BusKill/usb-a-magnetic-breakaway/Goldfishlaser Version/CAD Files/usbamagb_v03.1b.png

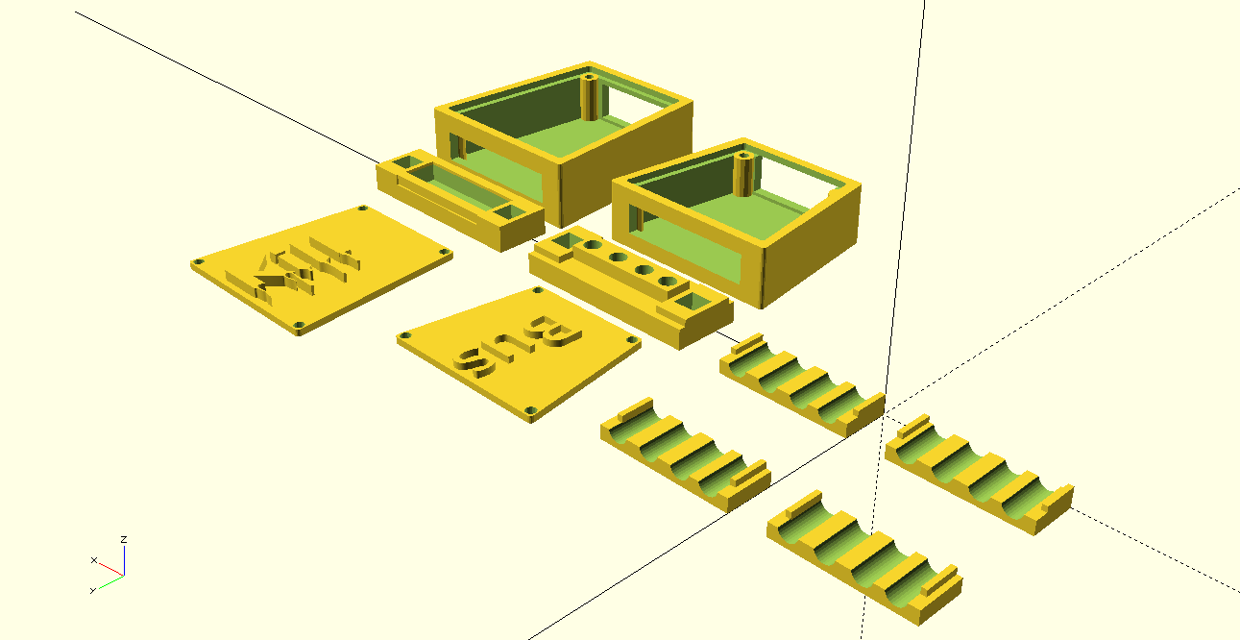
Goldfishlaser Version/CAD Files/usbamagb_v03.1b.png
