BusKill/usb-a-magnetic-breakaway/supplier/shenzen_qh_industrial_co/2021-05-24/una2.png

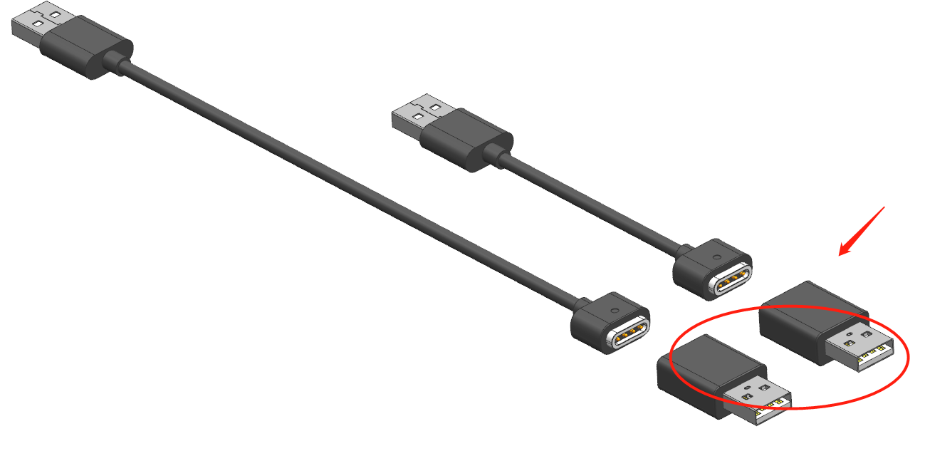
supplier/shenzen_qh_industrial_co/2021-05-24/una2.png
