BusKill/usb-a-magnetic-breakaway/supplier/shenzen_qh_industrial_co/2021-06-10/buskill_custom_female_3d_screenshot.jpg

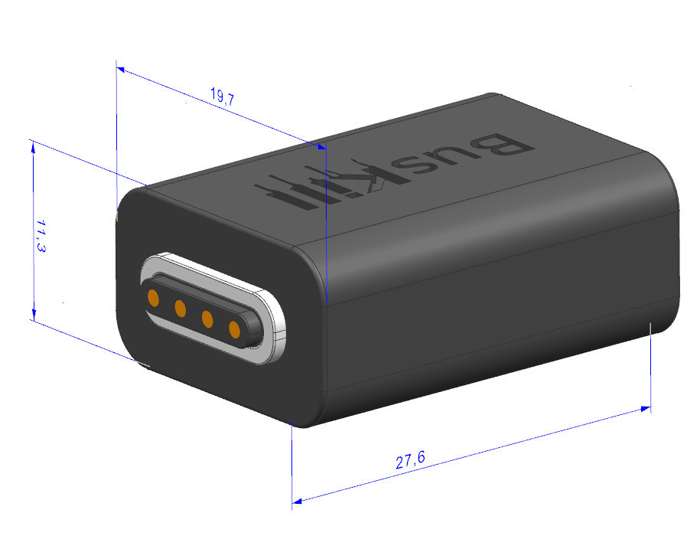
supplier/shenzen_qh_industrial_co/2021-06-10/buskill_custom_female_3d_screenshot.jpg
