BusKill/usb-a-magnetic-breakaway/supplier/shenzen_qh_industrial_co/2021-10-06/20211006_buskill_mold.jpg

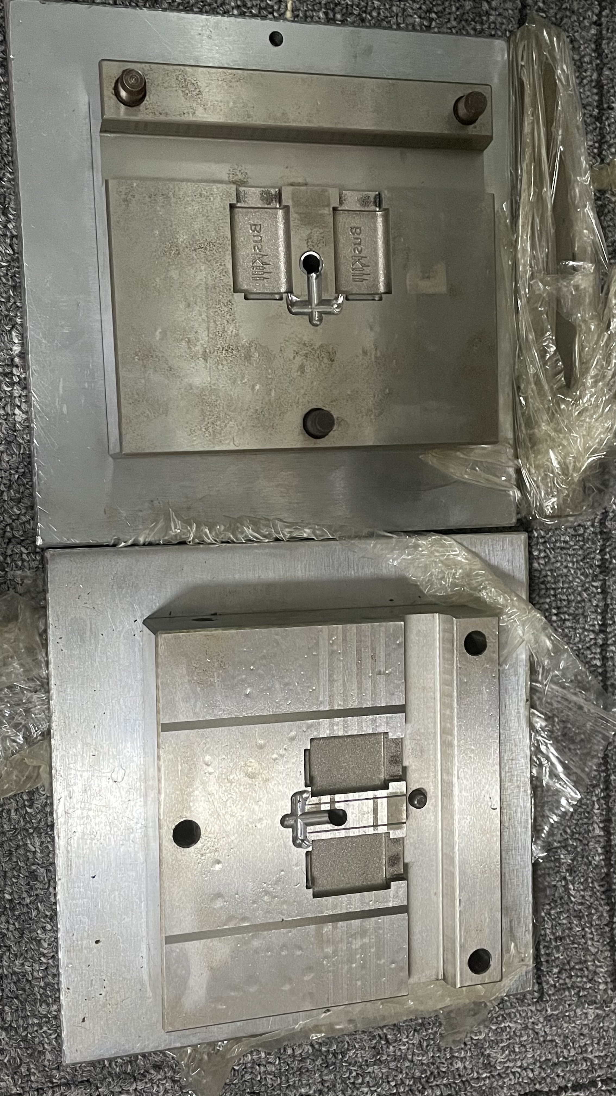
supplier/shenzen_qh_industrial_co/2021-10-06/20211006_buskill_mold.jpg
