BusKill/usb-a-magnetic-breakaway/supplier/shenzen_qh_industrial_co/2021-12-04/202112_buskill_sample1b.jpg

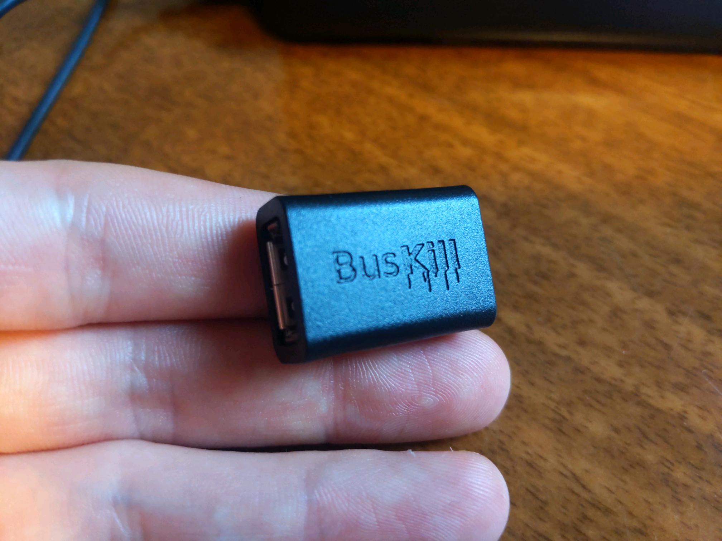
supplier/shenzen_qh_industrial_co/2021-12-04/202112_buskill_sample1b.jpg
