BusKill/usb-a-magnetic-breakaway/supplier/shenzen_qh_industrial_co/2025-02/2025-02_buskill-usb-c-cable.jpg

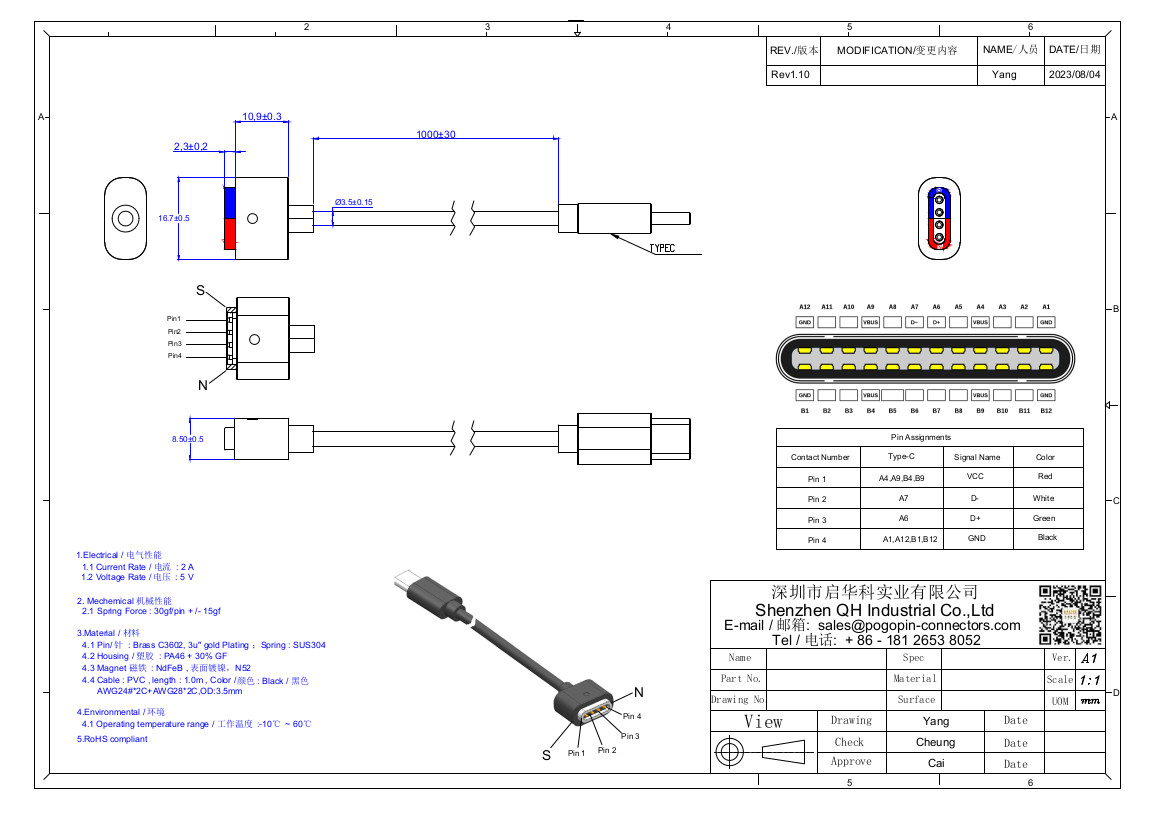
supplier/shenzen_qh_industrial_co/2025-02/2025-02_buskill-usb-c-cable.jpg
