BusKill/usb-a-magnetic-breakaway/supplier/shenzhen_eonline_industrial_co/eonline_catalog_202106.jpg

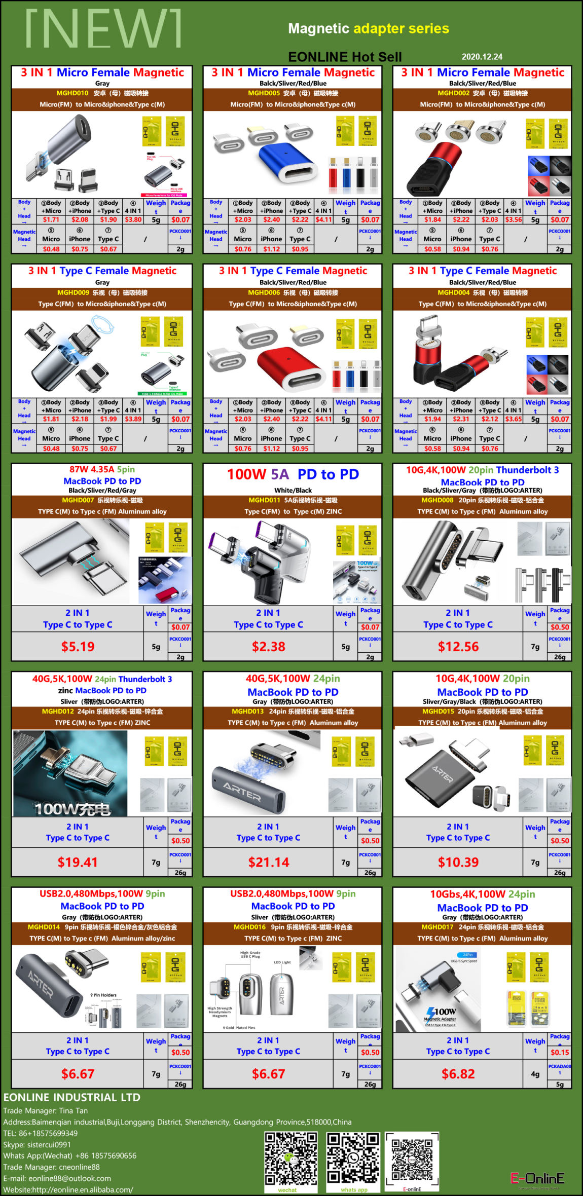
supplier/shenzhen_eonline_industrial_co/eonline_catalog_202106.jpg
