BusKill/usb-a-magnetic-breakaway/Goldfishlaser Version/CAD Files/intermediary print files/pogo_pin.stl

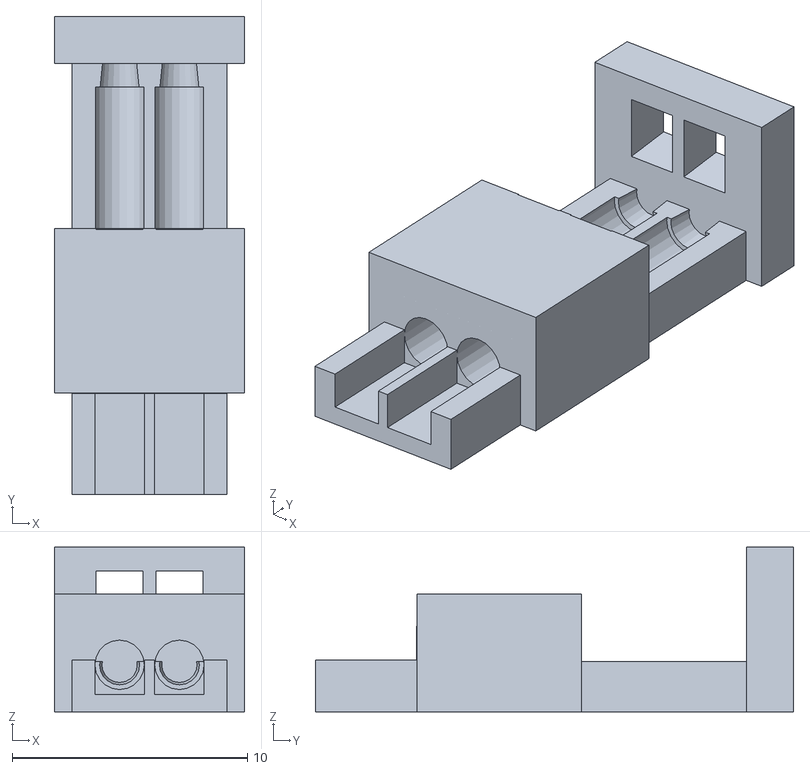
[picture p36: CAD file, 2020-09-26]
Goldfishlaser Version/CAD Files/intermediary print files/pogo_pin.stl
8.08 x 20.3 x 7.00
