BusKill/usb-a-magnetic-breakaway/digitalAssets/cad/cable/AS-BKA-CUP-001.FCStd

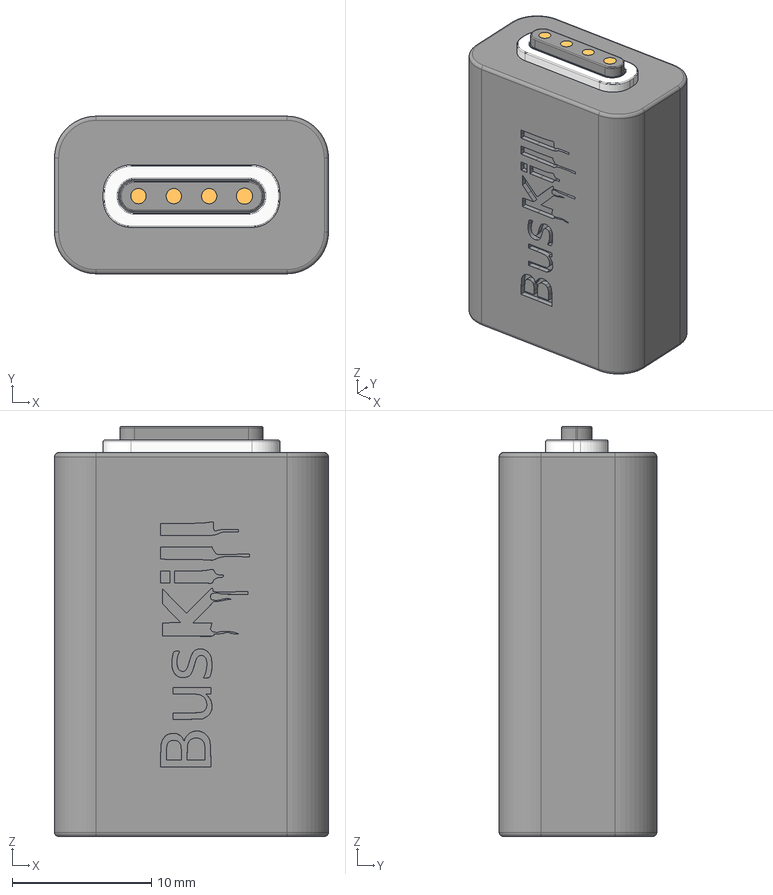
[picture p37: CAD file, 2026-05-12]
digitalAssets/cad/cable/AS-BKA-CUP-001.FCStd
19.7 x 11.3 x 29.5 mm
50u_pin003
50u_pin002
50u_pin004
50u_pin001
housing
magnet
overmold
usb
