BusKill/usb-a-magnetic-breakaway/Goldfishlaser Version/CAD Files/intermediary print files/magnet.stl

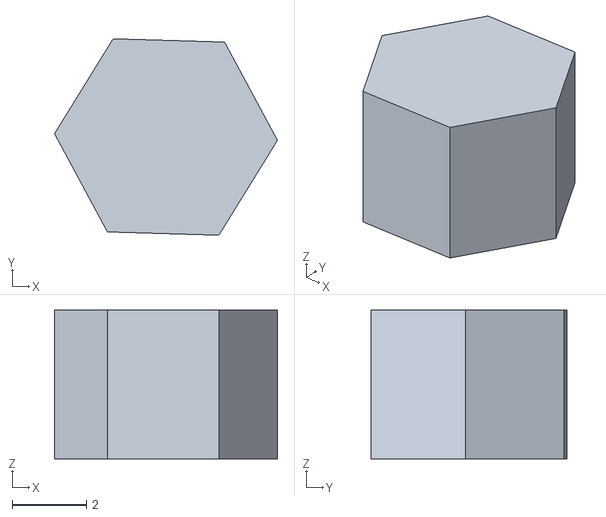
[picture p38: CAD file, 2020-09-19]
Goldfishlaser Version/CAD Files/intermediary print files/magnet.stl
6.00 x 5.28 x 4.00
