BusKill/usb-a-magnetic-breakaway/Goldfishlaser Version/CAD Files/intermediary design files/cubeface_v03.9.stl

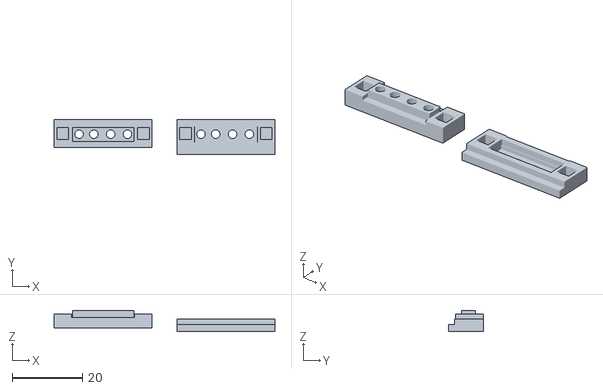
[picture p39: CAD file, 2023-10-10]
Goldfishlaser Version/CAD Files/intermediary design files/cubeface_v03.9.stl
63.0 x 10.0 x 6.00
