BusKill/usb-a-magnetic-breakaway/Goldfishlaser Version/CAD Files/intermediary design files/usbamagb_v03.8.stl

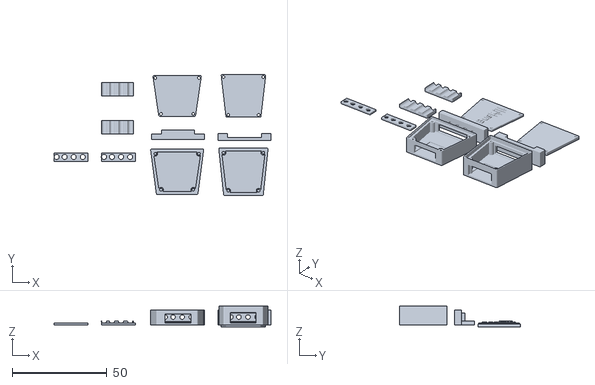
[picture p40: CAD file, 2023-10-04]
Goldfishlaser Version/CAD Files/intermediary design files/usbamagb_v03.8.stl
114.5 x 63.7 x 11.0
