BusKill/usb-a-magnetic-breakaway/digitalAssets/cad/cable/buskill_usba_magnetic_breakaway_cable.FCStd

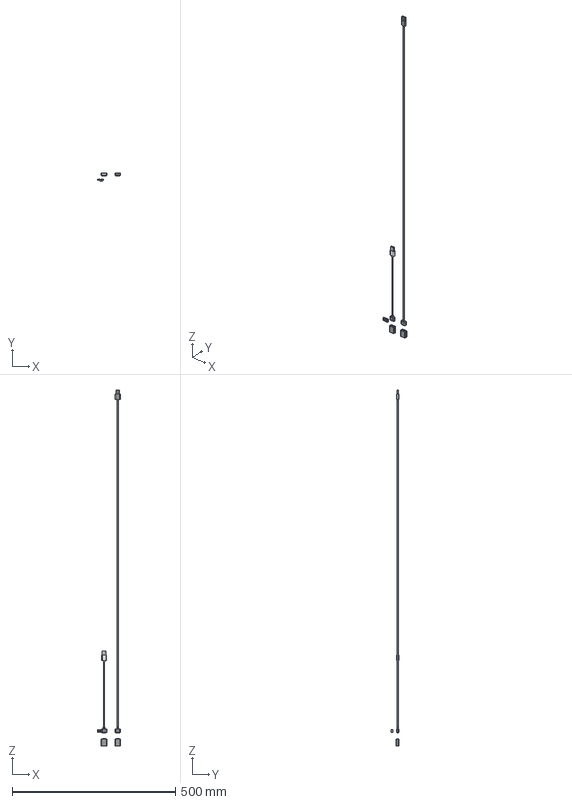
[picture p41: CAD file, 2021-05-31]
digitalAssets/cad/cable/buskill_usba_magnetic_breakaway_cable.FCStd
71.5 x 26.0 x 1091.2 mm
pogo pin
MAGNET - 2
Housing - 2
pogo pin001
pogo pin002
pogo pin003
In mold
Out mold
50u_ PIN (6) (4)
MAGNET
50u_ PIN (6) (4)001
50u_ PIN (6) (4)002
Housing (2)
50u_ PIN (6) (4)003
overmold
pogo pin004
MAGNET - 003
Housing - 003
pogo pin005
pogo pin006
pogo pin007
In mold001
Out mold001
Cable1
Cable2
50u_ PIN (6) (4)004
MAGNET001
50u_ PIN (6) (4)005
50u_ PIN (6) (4)006
Housing (2)001
50u_ PIN (6) (4)007
overmold001
B
U
S
K
I_1
I_2
L_1
L_2
