BusKill/usb-a-magnetic-breakaway/Goldfishlaser Version/CAD Files/intermediary design files/dengineering_v02.3.8.stl

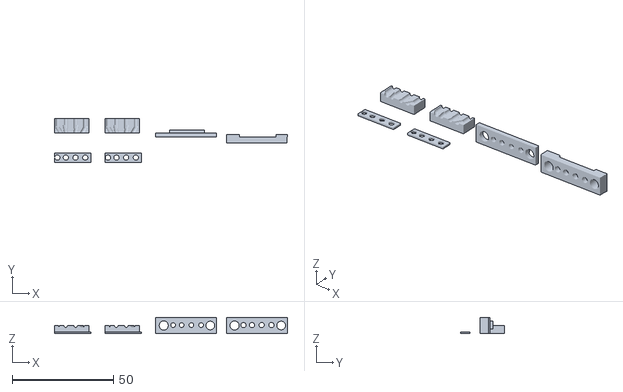
[picture p42: CAD file, 2023-07-01]
Goldfishlaser Version/CAD Files/intermediary design files/dengineering_v02.3.8.stl
115.2 x 21.5 x 8.00
