BusKill/usb-a-magnetic-breakaway/Goldfishlaser Version/CAD Files/intermediary design files/mag_startover_v0.2.stl

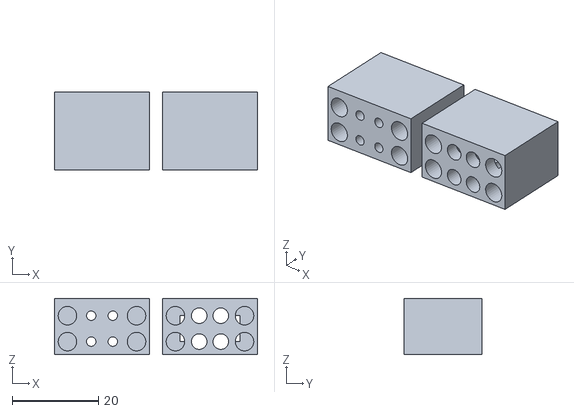
[picture p43: CAD file, 2023-05-12]
Goldfishlaser Version/CAD Files/intermediary design files/mag_startover_v0.2.stl
47.0 x 18.0 x 13.0
