BusKill/usb-a-magnetic-breakaway/Goldfishlaser Version/CAD Files/intermediary design files/magnetic_release_v0.9.stl

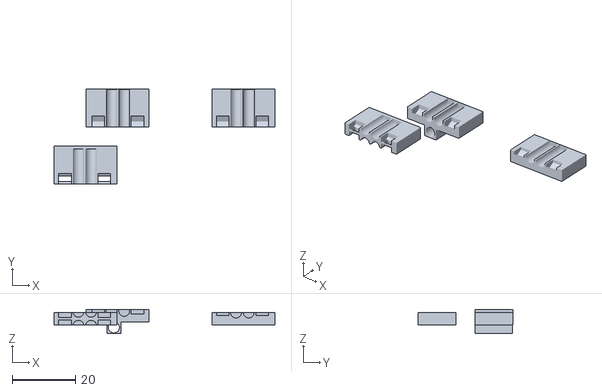
[picture p44: CAD file, 2023-05-04]
Goldfishlaser Version/CAD Files/intermediary design files/magnetic_release_v0.9.stl
70.1 x 30.0 x 7.75
