BusKill/usb-a-magnetic-breakaway/Goldfishlaser Version/CAD Files/intermediary design files/magnetic_release_B_v0.9.stl

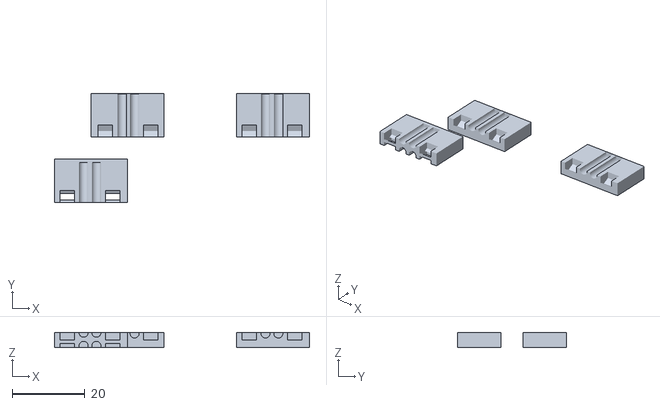
[picture p45: CAD file, 2023-02-24]
Goldfishlaser Version/CAD Files/intermediary design files/magnetic_release_B_v0.9.stl
70.1 x 30.0 x 4.00
