BusKill/usb-a-magnetic-breakaway/Goldfishlaser Version/CAD Files/intermediary design files/magnetic_release_R_v09.stl

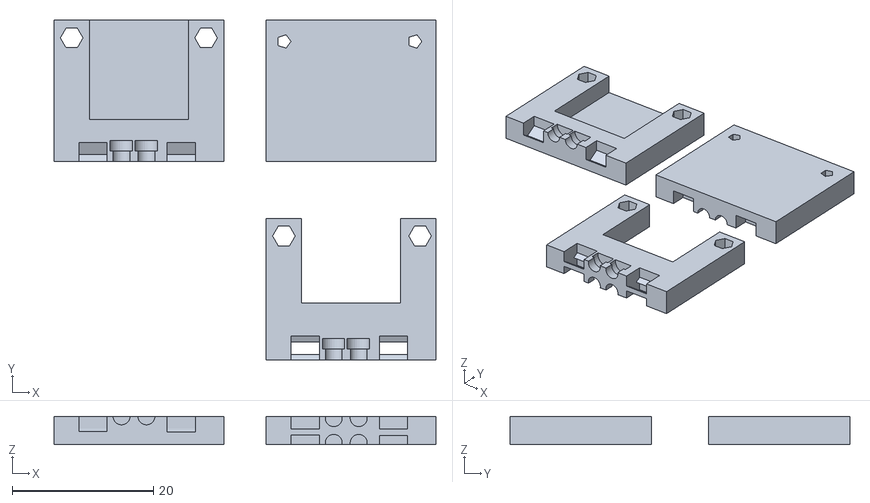
[picture p46: CAD file, 2023-02-20]
Goldfishlaser Version/CAD Files/intermediary design files/magnetic_release_R_v09.stl
54.0 x 48.0 x 4.00
